shelbeeely/Fairberry/BBQ10/configuration.h

/*
 * ## Mainboard type
 * Can be either of the following:
 * FAIRBERRY_V0_3_0 : This is the custom mainboard, version 0.3.0
 * FAIRBERRY_V0_2_0 : This is the custom mainboard, version 0.2.0
 * FAIRBERRY_V0_1_1 : This is the custom mainboard, version 0.1.1
 * ARDUINO : The original option, using an Arduino Pro Micro
 * BEETLE : A slightly different version of the original option, using a smaller Beetle board based on the ATMega32u4. Not recommeded, because the beetle has one to few pins, so you have to solder directly to the ATMega32u4.
 * ESP32: Using an ESP32-based board to couple the board using Bluetooth. Power management is still rough (see the power saving options below) and it draws more current than the Arduino path. This is the recommended option for Free Ink SDK devices like the Xteink X4/X4 Classic: the SDK has a purpose-built BLE keyboard host library (BleKeyboardHost / lib-ble, https://freeink.org/docs/lib-ble) that works on ESP32-C3 and ESP32-S3. It's an opt-in firmware capability (FREEINK_CAP_BLE_HID_HOST) though, so confirm the specific firmware image on your device has it enabled before counting on this.
 * FAIRBERRY_ESP32S3_SMART: A standalone, battery-powered ESP32-S3 board -- keyboard + trackball + mic/speaker/microSD + WiFi voice transcription. Pairs wirelessly with the X4 (or any BLE HID host) instead of physically attaching to it. See Documentation/Hardware_Standalone_Smart_Keyboard.md. This is the option for the mic/speaker/WiFi/Whisper features further down this file -- they're not wired up for plain BOARD_TYPE ESP32.
 */
#define BOARD_TYPE FAIRBERRY_V0_3_0

/*
 * ## Power Saving
 * Without power saving options the whole device consumes around 60mA.
 * While it's active, that's fine, but it consumes the same amount of
 * energy while it's idle. Since the device is idle for most of the time,
 * reducing the idle power is important.
 * 
 * For this there are multiple options:
 * 
 * ### IDLE_TIMEOUT
 * This is the basic setting that determines after how many ms
 * powersaving features are triggered. If the device was idle for more
 * than the given time, the keyboard backlight is disabled and the given
 * power save mode is applied (if any).
 * 
 * ### POWERSAVE_ARDUINO_IDLE
 * This is the recommended powersaving mode for BOARD_TYPE ARDUINO. It's a light sleep that keeps
 * the USB connection active. It saves around 40mA. It introduces a delay
 * of up to 120ms when the device is woken up.
 * 
 * ### POWERSAVE_ARDUINO_POWERDOWN
 * This is the more aggressive powersaving method for BOARD_TYPE ARDUINO. It completely turns off
 * the microcontroller, saving around 55mA. This takes the power consumption
 * down to almost nothing, but USB needs to reconnect after the keyboard
 * is woken up. This takes about 1-2 seconds.
 * 
 * ### POWERSAVE_ESP32_LOGHT_SLEEP
 * This is the recommended powersaving mode for BOARD_TYPE ARDUINO. It's a light sleep that keeps
 * the Bluetooth connection active. It reduces the power consumption from around 160mA to about 20mA when not active.
 * It introduces a delay of up to 50ms when the device is woken up.
 * 
 * For Arduino boards you can use either POWERSAVE_ARDUINO_IDLE or POWERSAVE_ARDUINO_POWERDOWN or none, but not both.
 * 
 * For ESP32 boards you can either use POWERSAVE_ESP32_LIGHT_SLEEP or none.
 */
#define IDLE_TIMEOUT 30L * 1000L
#define POWERSAVE_ARDUINO_IDLE
//#define POWERSAVE_ARDUINO_IDLE_DURING_ACTIVE
//#define POWERSAVE_ARDUINO_CLOCKDOWN
//#define POWERSAVE_ARDUINO_POWERDOWN
//#define POWERSAVE_ESP32_LIGHT_SLEEP
//#define POWERSAVE_ESP32_DEEP_SLEEP

//#define ARDUINO_CLOCKDOWN_DIVISION 8


/*
 * To visually show that the device is in cursor mode, the keyboard backlight
 * will blink rapidly if BLINK_IN_CURSOR_MODE is set. Change BLINK_TIMEOUT
 * to change the blinking frequency.
 * 
 * If you are using a fairberry mainboard, you can use LED0_IN_CURSOR_MDOE
 * instead of BLINK_IN_CURSOR_MODE, to have the LED0 glow when in cursor mode (doesn't blink).
 */
#define BLINK_IN_CURSOR_MODE
#define BLINK_TIMEOUT 20L
//#define LED0_IN_CURSOR_MODE

/*
 * 
 */
#define STICKY_SYM
#define STICKY_LSH
#define STICKY_RSH
#define STICKY_CTRL
#define STICKY_ALT
#define DOUBLETAP_LOCK_SYM
#define DOUBLETAP_LOCK_LSH
#define DOUBLETAP_LOCK_RSH
//#define DOUBLETAP_LOCK_CTRL
//#define DOUBLETAP_LOCK_ALT

#define DEBOUNCE_MS 50

/*
 * If you define DEBUG_SERIAL_INSTEAD_OF_USB, the device will not function as a keyboard, but instead
 * output key presses to serial. Used for debugging.
 */
//#define DEBUG_SERIAL_INSTEAD_OF_USB

/*
 * Default brightness of the keys when active. Possible values: 0-255
 */
#define DEFAULT_KEYBOARD_BRIGHTNESS 60

/*
 * Enables serial debug logging. Only activate when debugging.
 */
//#define SERIAL_DEBUG_LOG

/*
 * ## Trackball (ICSH044A / SparkFun BlackBerry Trackballer Breakout clone)
 * Implemented for BOARD_TYPE ESP32 and FAIRBERRY_ESP32S3_SMART. See
 * boards.h for the pin assignment (different per board type) and
 * trackball.h for the reading/debounce logic. Wiring/BOM details are in
 * Documentation/Hardware_ESP32_Trackball_Mainboard.md (pull-up resistors,
 * LED current-limiting, physical mounting) and
 * Documentation/Hardware_Standalone_Smart_Keyboard.md for the S3 board.
 *
 * Movement is read as raw hall-sensor edges and turned into arrow-key
 * taps once TRACKBALL_EDGES_PER_STEP edges accumulate on an axis; the
 * center click sends TRACKBALL_BTN_KEY (both configurable below, or left
 * at their defaults in trackball.h). This hasn't been validated against
 * real hardware yet -- treat the pin map and thresholds as a starting
 * point, not a tested value.
 */
//#define TRACKBALL_ENABLED
//#define TRACKBALL_LED_ENABLED // Also drive the trackball's RGB backlight
//#define TRACKBALL_EDGES_PER_STEP 4
//#define TRACKBALL_BTN_KEY KEY_RETURN

/*
 * ## Voice notes + WiFi transcription (BOARD_TYPE FAIRBERRY_ESP32S3_SMART only)
 * See Documentation/Hardware_Standalone_Smart_Keyboard.md for the full
 * picture. Summary: AUDIO_ENABLED turns on local mic recording (to WAV on
 * the SD card) and speaker playback/confirmation tones -- this works fully
 * offline. WIFI_TRANSCRIPTION_ENABLED additionally connects to WiFi
 * periodically and uploads any recordings that don't have a matching .txt
 * yet to the OpenAI Whisper API, saving the returned transcript back to
 * the SD card. There is no on-device speech recognition -- transcription
 * requires WiFi and a paid OpenAI API key, and only happens when a sync
 * runs (manual trigger or once a day), not in real time.
 *
 * Requires BBQ10/secrets.h with your WiFi credentials and OpenAI API key
 * -- copy secrets.h.example and fill it in. secrets.h is gitignored;
 * never commit real credentials.
 *
 * Requires the ArduinoJson library in addition to the ones listed in
 * Documentation/Hardware_Fairberry_Mainboard.md.
 *
 * TRANSFER_MODE_ENABLED adds a separate, local-only feature: SYM + T
 * toggles a local web server (no cloud, no API key) for browsing and
 * downloading recordings/transcripts from a browser on the same WiFi
 * network. Independent of WIFI_TRANSCRIPTION_ENABLED -- you can have
 * either, both, or neither. Since this device has no screen, turning
 * transfer mode on types its local URL as keystrokes into whatever's
 * focused on the paired host rather than displaying it anywhere -- see
 * web_server.h.
 *
 * VOICE_TYPING_ENABLED is a third, different mode: SYM + V starts/stops
 * a short recording, and stopping it immediately (not batched) uploads
 * to Whisper, reads the transcript back out loud via the OpenAI TTS API
 * so you can verify it heard you right, then waits for Enter (type it
 * into the host) or Backspace (discard). This is the "voice typing,
 * verify before sending" flow, separate from the batch sync above (which
 * is better suited to longer recordings you don't want to wait on). Runs
 * blocking -- see the comment at the top of voice_typing.h for what that
 * means in practice. Also needs BBQ10/secrets.h (same OpenAI API key,
 * it's used for both Whisper and TTS).
 */
//#define AUDIO_ENABLED
//#define WIFI_TRANSCRIPTION_ENABLED // Requires AUDIO_ENABLED and BBQ10/secrets.h
//#define TRANSFER_MODE_ENABLED // Requires AUDIO_ENABLED and BBQ10/secrets.h (WiFi credentials only, no API key needed for this one)
//#define VOICE_TYPING_ENABLED // Requires AUDIO_ENABLED and BBQ10/secrets.h
#define WHISPER_SYNC_INTERVAL_MS (24L * 60L * 60L * 1000L) // Once a day
#if defined(WIFI_TRANSCRIPTION_ENABLED) || defined(TRANSFER_MODE_ENABLED) || defined(VOICE_TYPING_ENABLED)
  #include "secrets.h"
#endif
